kaeverens/waterbot/tracks/track-dock.FCStd

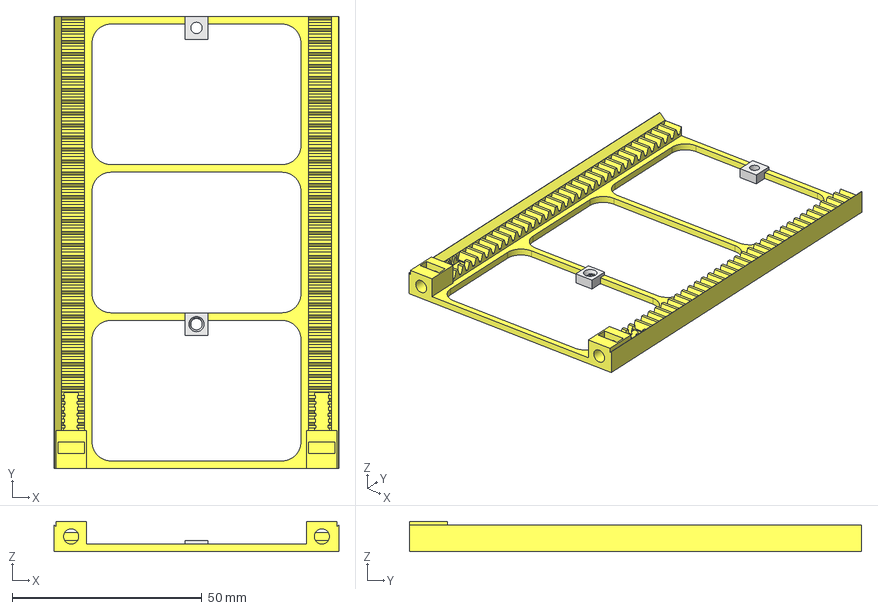
[picture p15: CAD file, 2021-03-06]
tracks/track-dock.FCStd
75.0 x 119.0 x 8.00 mm
track
