kaeverens/waterbot/bot/v3/syringe/syringe-barrel_strap.stl

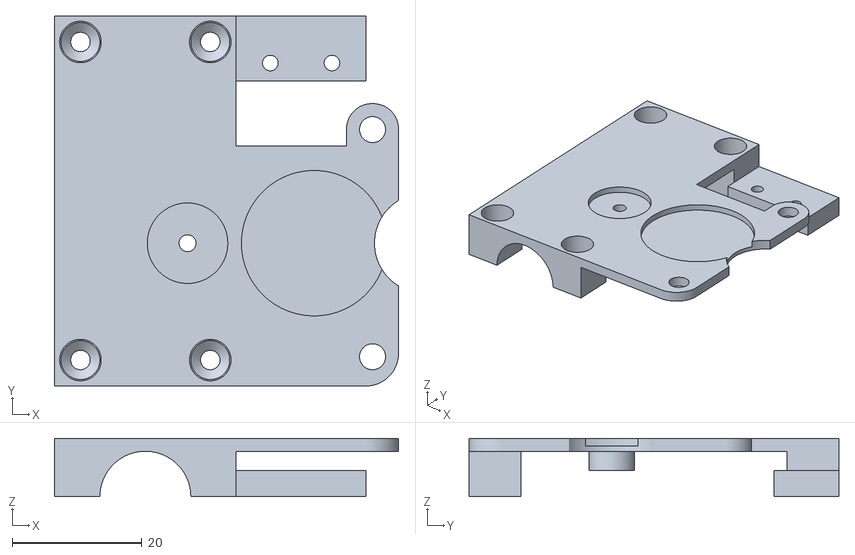
[picture p16: CAD file, 2021-03-21]
bot/v3/syringe/syringe-barrel_strap.stl
53.0 x 57.0 x 9.00
