kaeverens/waterbot/tracks/track-120mm.stl

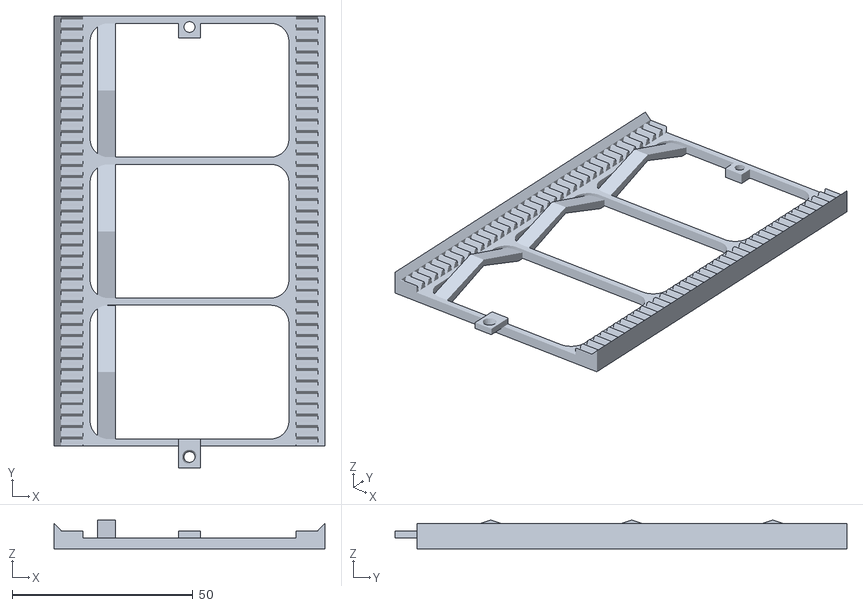
[picture p17: CAD file, 2021-03-06]
tracks/track-120mm.stl
75.0 x 125.0 x 8.00
