kaeverens/waterbot/bot/v3/syringe/syringe.FCStd

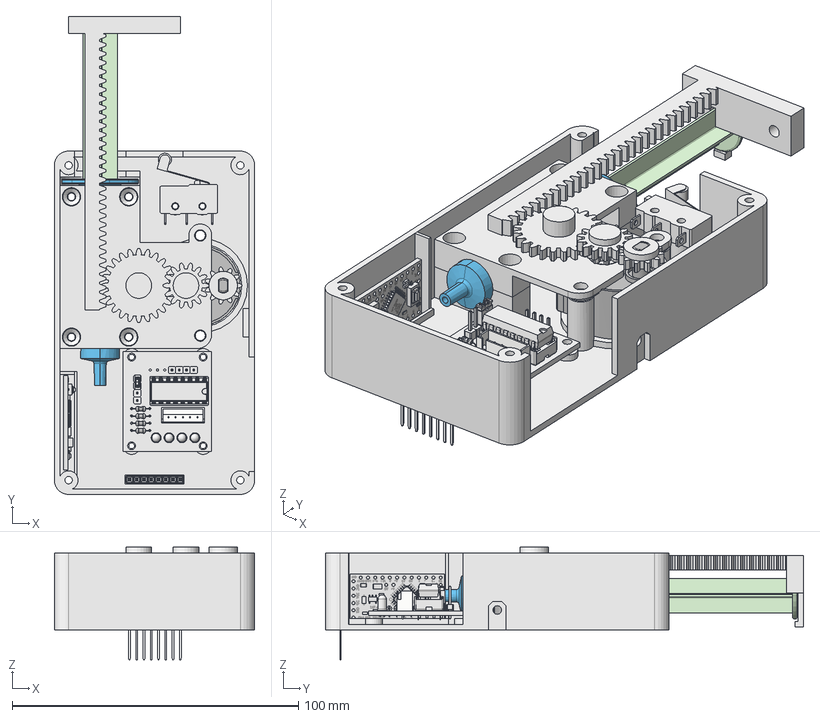
[picture p18: CAD file, 2021-03-13]
bot/v3/syringe/syringe.FCStd
70.0 x 167.0 x 39.5 mm
28BYJ-48-stepper
5ml HSW barrel
5ml HSW plunger
pcb
jumper_connector
r205
r206
r207
r208
conn_lead
conn_lead001
conn_lead002
conn_lead003
conn_lead004
spacer
pin
spacer001
pin001
spacer002
pin002
spacer003
pin003
spacer (1)
pin (1)
spacer (1)001
pin (1)001
spacer (1)002
pin (1)002
spacer (1)003
pin (1)003
LED 3mm
LED 3mm001
LED 3mm002
LED 3mm003
package
lead
housing
pins
Pro-Mini
Limit Switch 2
SIL_Socket_Body
SIL_SocketPin
SIL_Socket_Body001
SIL_SocketPin001
SIL_Socket_Body002
SIL_SocketPin002
SIL_Socket_Body003
SIL_SocketPin003
SIL_Socket_Body004
SIL_SocketPin004
SIL_Socket_Body005
SIL_SocketPin005
SIL_Socket_Body006
SIL_SocketPin006
SIL_Socket_Body007
SIL_SocketPin007
